pranabendra/digital-pid-controller/Circuit Diagrams/Digital_PID_bb.png

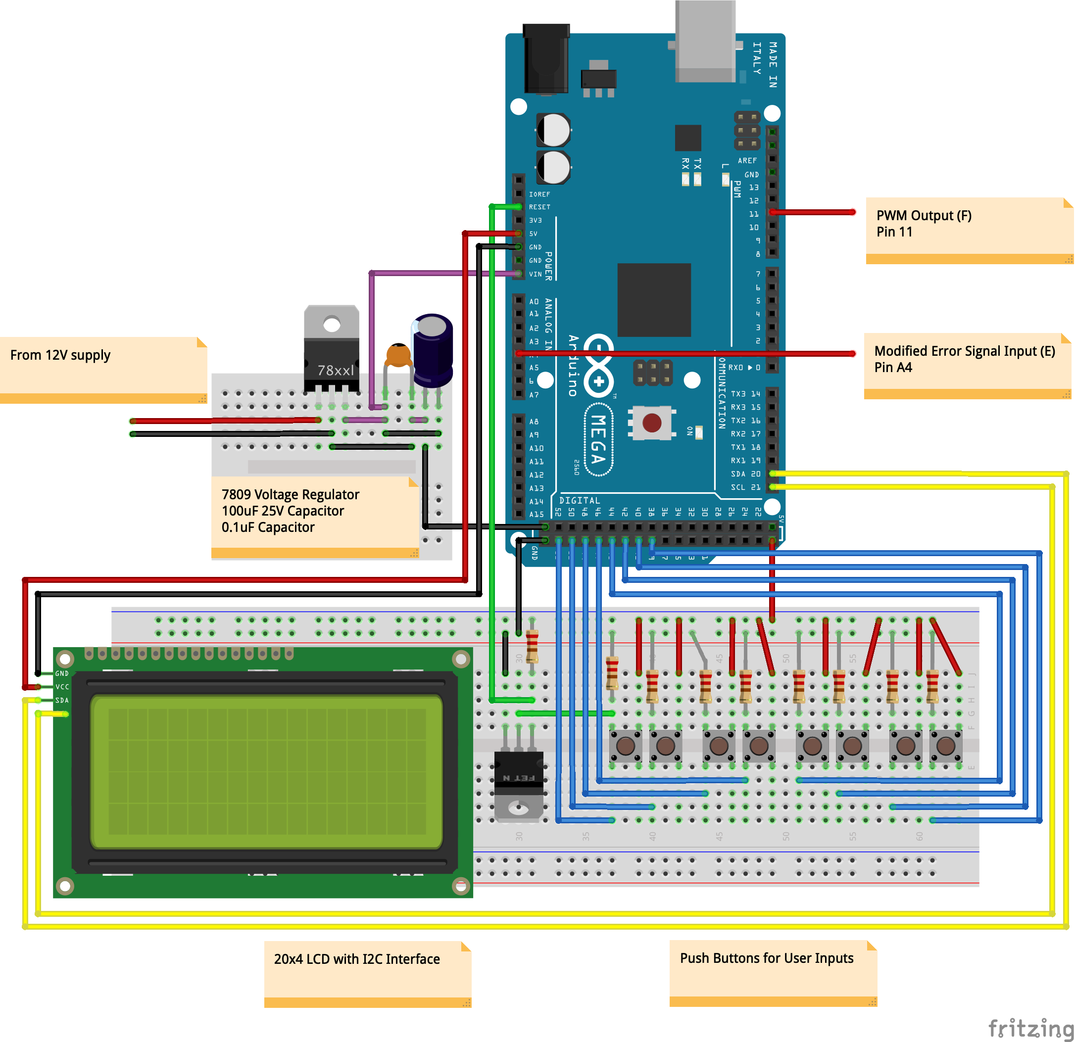
Circuit Diagrams/Digital_PID_bb.png
