pranabendra/digital-pid-controller/Circuit Diagrams/Input Circuit.png

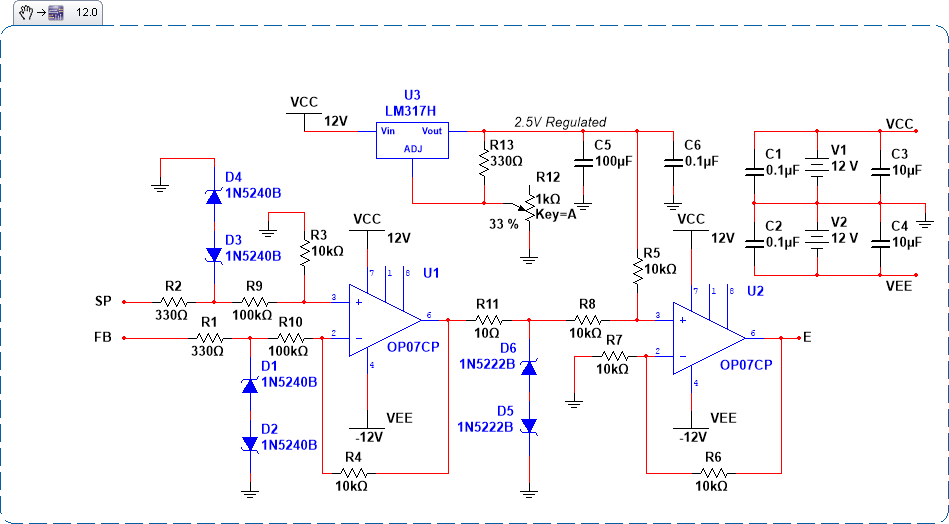
Circuit Diagrams/Input Circuit.png
