pranabendra/digital-pid-controller/Circuit Diagrams/Output Circuit.png

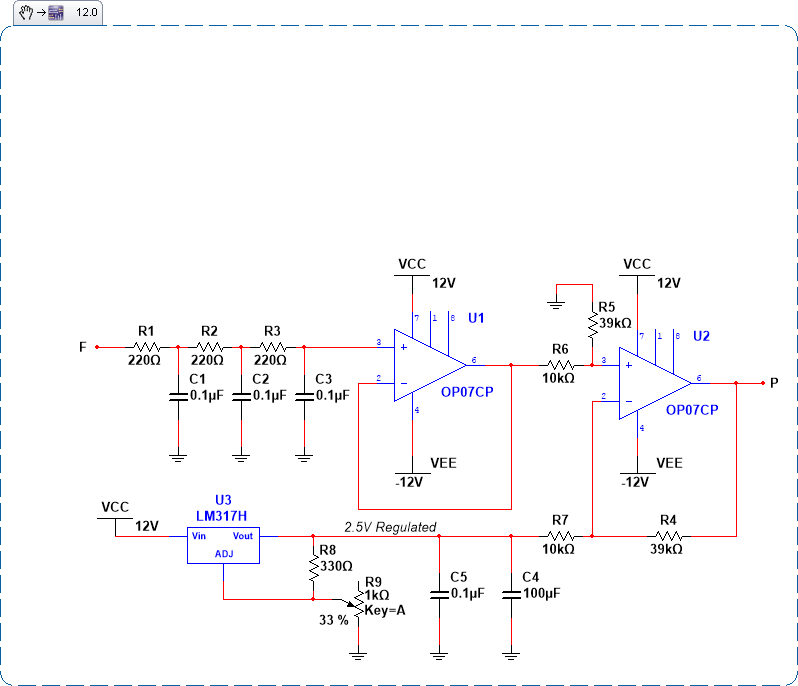
Circuit Diagrams/Output Circuit.png
