pranabendra/digital-pid-controller/Experiment Pictures/IMG_20191108_121836_LL.jpg

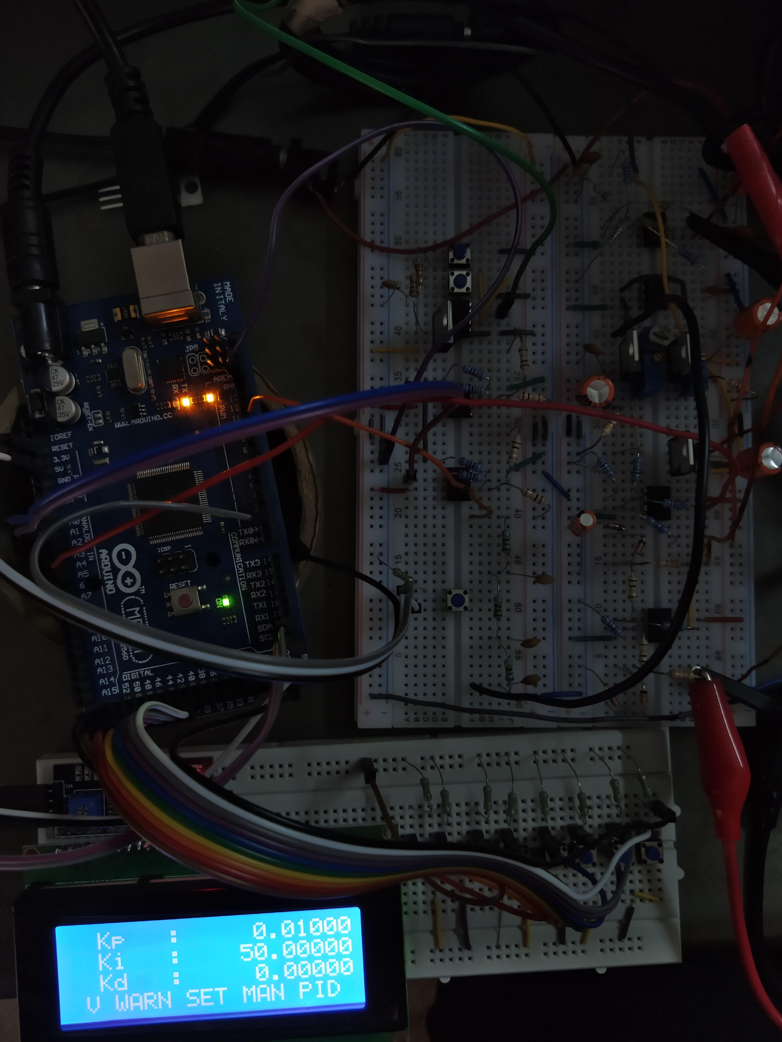
Experiment Pictures/IMG_20191108_121836_LL.jpg
