pranabendra/digital-pid-controller/Experiment Pictures/Screenshot_2019-11-15-19-36-52.jpg

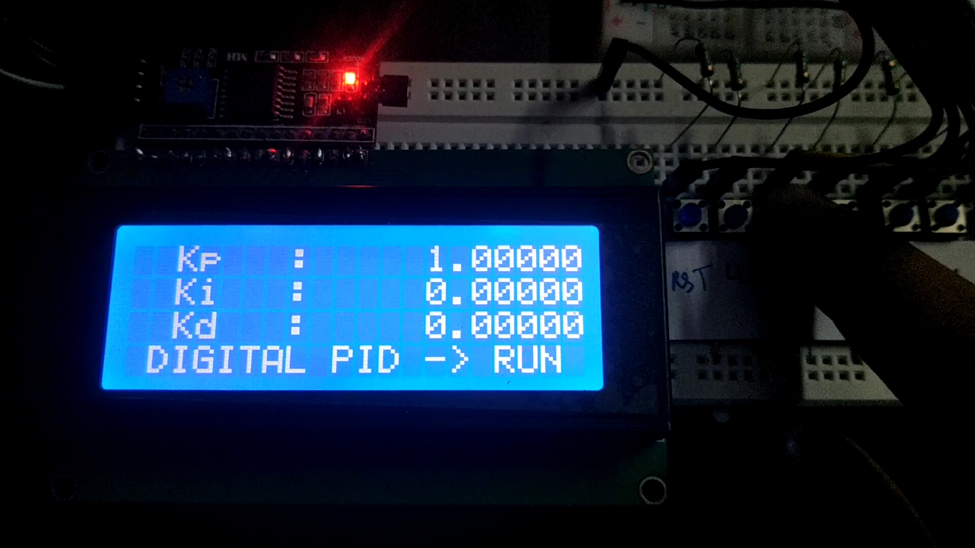
Experiment Pictures/Screenshot_2019-11-15-19-36-52.jpg
