pranabendra/digital-pid-controller/Experiment Pictures/Screenshot_2019-11-15-21-33-48.jpg

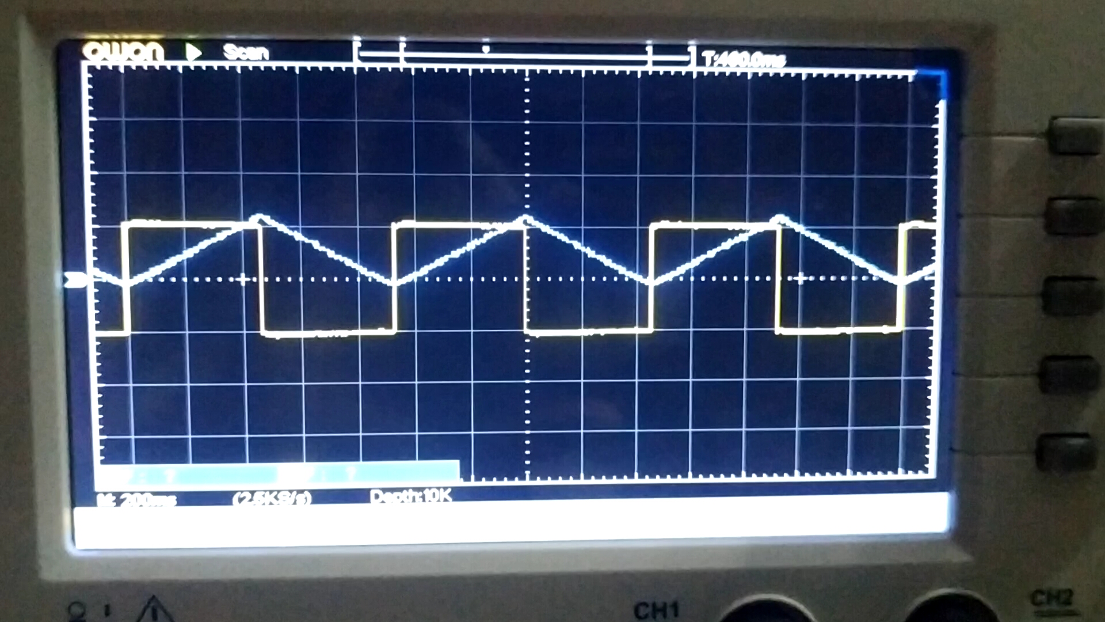
Experiment Pictures/Screenshot_2019-11-15-21-33-48.jpg
