pranabendra/digital-pid-controller/Experiment Pictures/Screenshot_2019-11-15-21-37-20.jpg

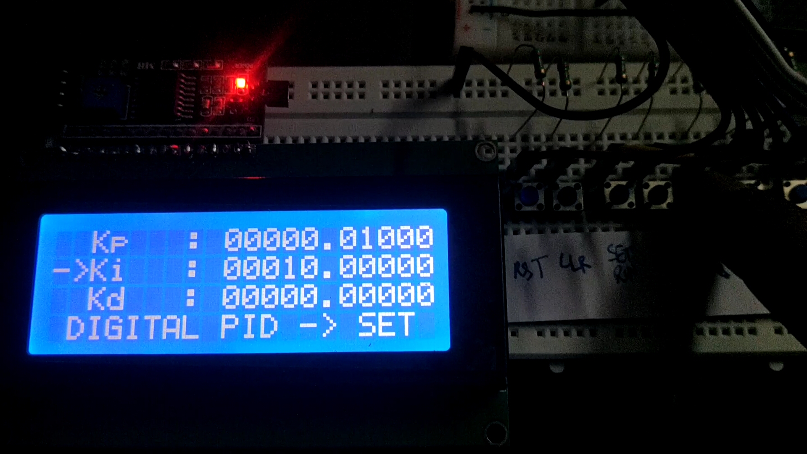
Experiment Pictures/Screenshot_2019-11-15-21-37-20.jpg
